floookay/barnacle/prototyping/layout.jpg

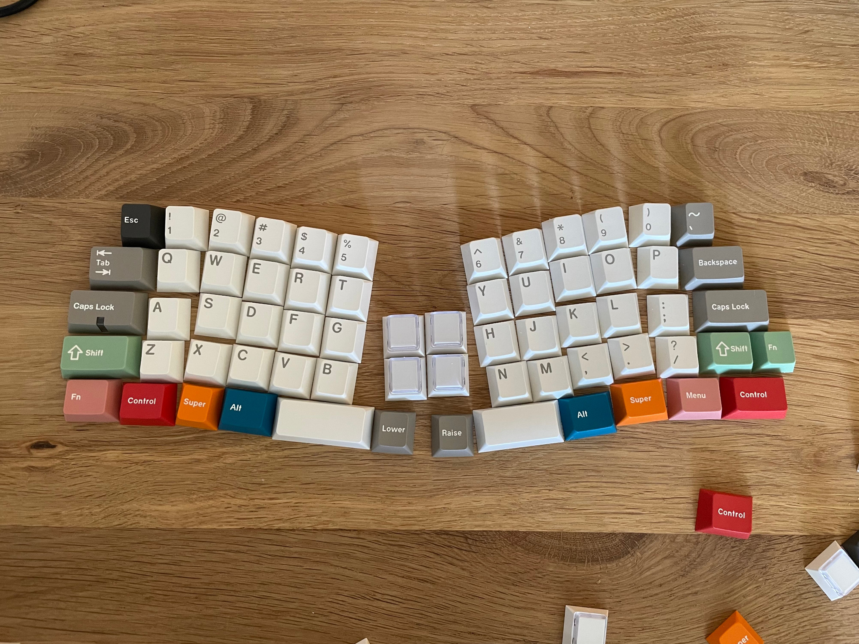
prototyping/layout.jpg
