floookay/barnacle/prototyping/plate_left_15.stl

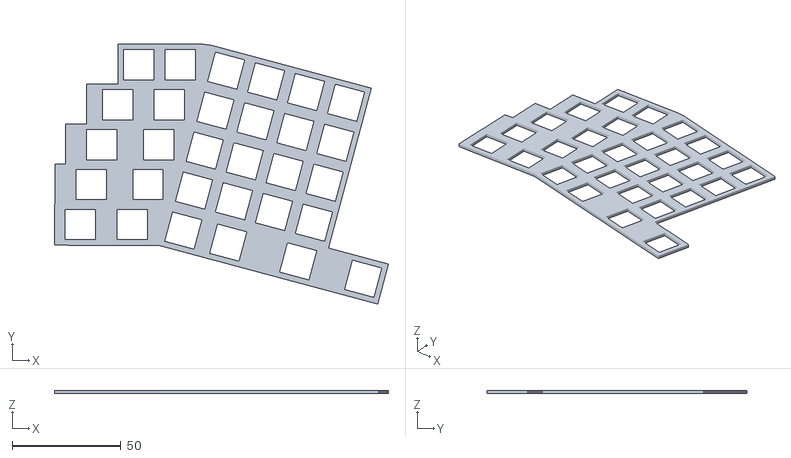
[picture p47: CAD file, 2024-06-17]
prototyping/plate_left_15.stl
153.8 x 119.8 x 1.60
