floookay/barnacle/prototyping/plate_middle.stl

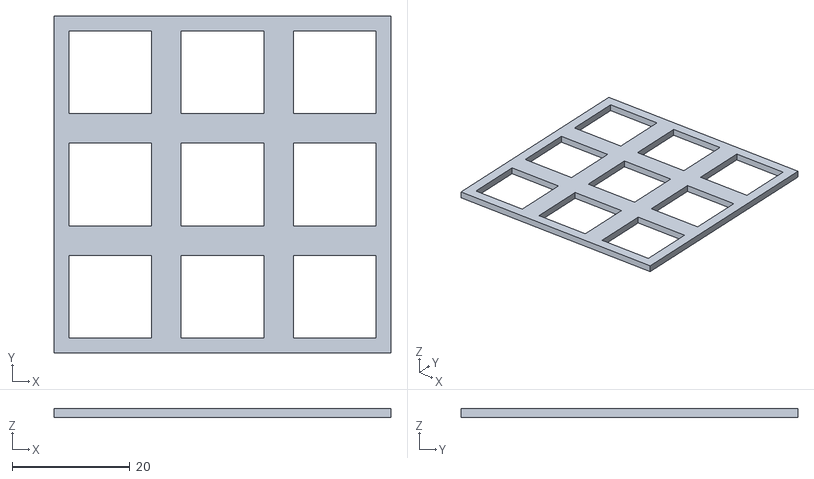
[picture p48: CAD file, 2024-06-17]
prototyping/plate_middle.stl
57.2 x 57.2 x 1.60
