floookay/barnacle/case/barnacle-shell.3mf

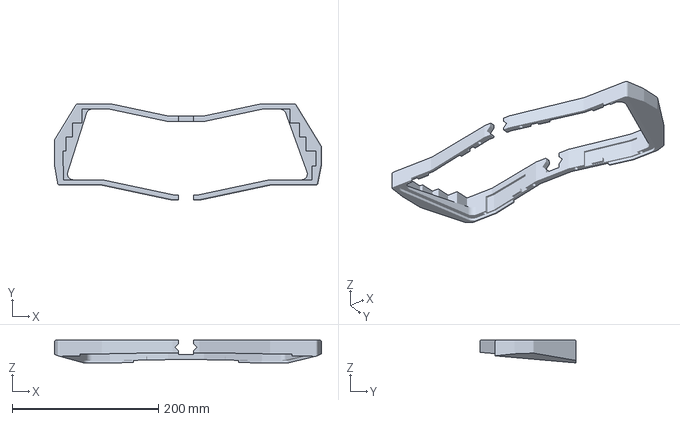
[picture p49: CAD file, 2024-09-08]
case/barnacle-shell.3mf
364.8 x 131.8 x 31.3 mm
