floookay/barnacle/case/barnacle-plate_right.3mf

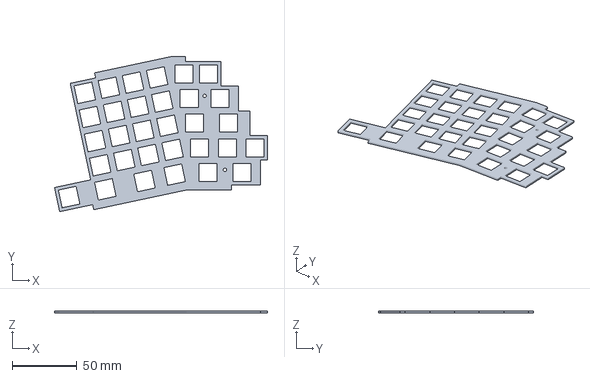
[picture p50: CAD file, 2024-08-31]
case/barnacle-plate_right.3mf
164.5 x 120.0 x 1.50 mm
