floookay/barnacle/case/barnacle-plate_fixer_bottom.3mf

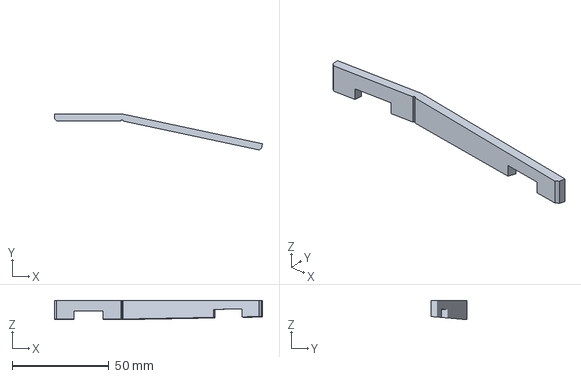
[picture p51: CAD file, 2024-08-31]
case/barnacle-plate_fixer_bottom.3mf
107.3 x 18.5 x 9.98 mm
