floookay/barnacle/case/barnacle-plate_fixer_top.3mf

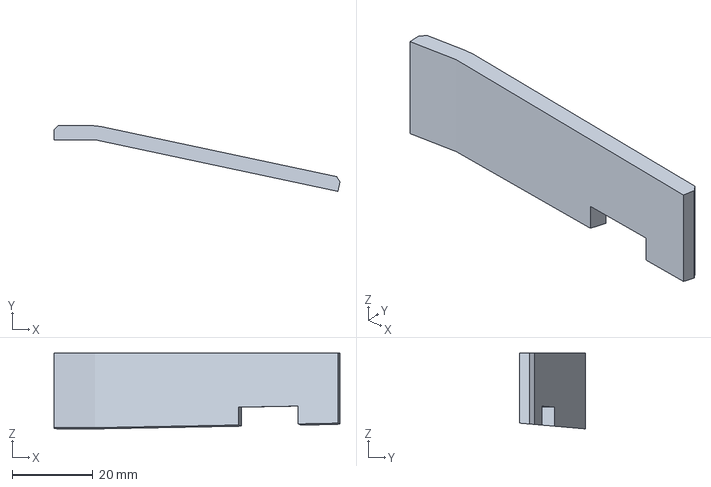
[picture p52: CAD file, 2024-08-31]
case/barnacle-plate_fixer_top.3mf
70.6 x 16.2 x 18.7 mm
