floookay/barnacle/case/barnacle-bottom_plate.dxf

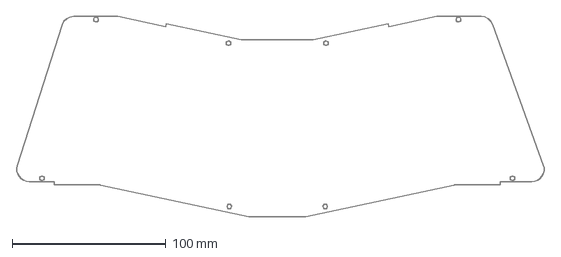
[picture p53: CAD file, 2024-08-26]
case/barnacle-bottom_plate.dxf
343.5 x 130.1 mm
